Envious-Data/Env-KB/_pictures/Rev.0/Built/DSC_0819.JPG

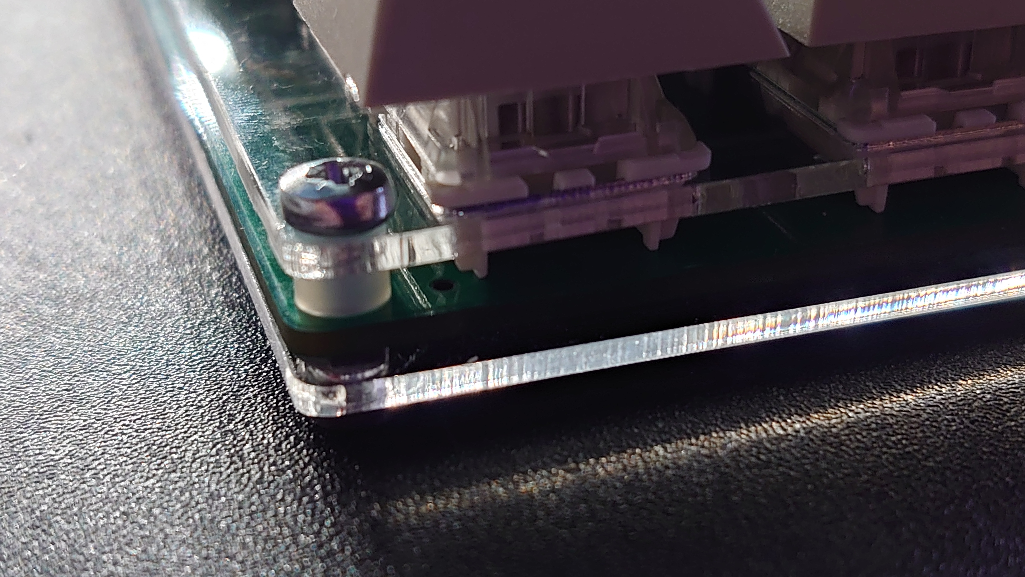
_pictures/Rev.0/Built/DSC_0819.JPG
