Envious-Data/Env-KB/_pictures/Rev.0/PCB2.JPG

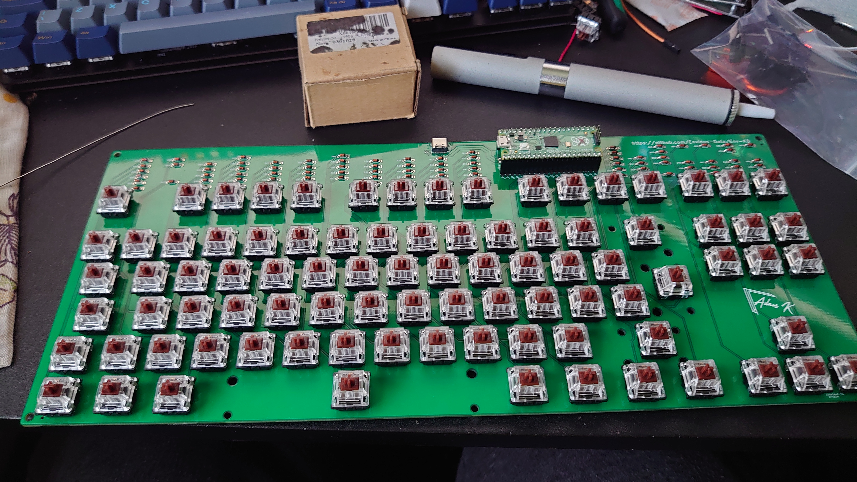
_pictures/Rev.0/PCB2.JPG
