Envious-Data/Env-KB/_pictures/Rev.0/PCB4.JPG

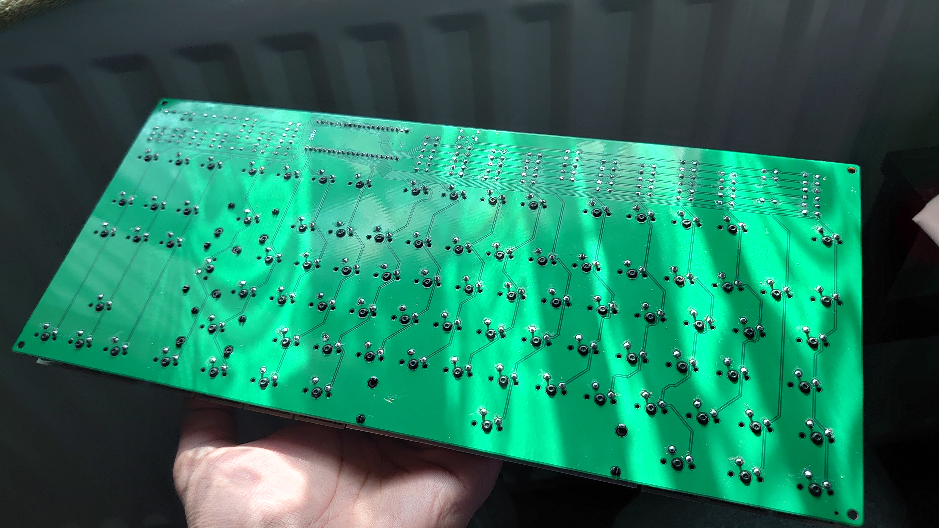
_pictures/Rev.0/PCB4.JPG
