Envious-Data/Env-KB/_pictures/Rev.0/PCB7.JPG

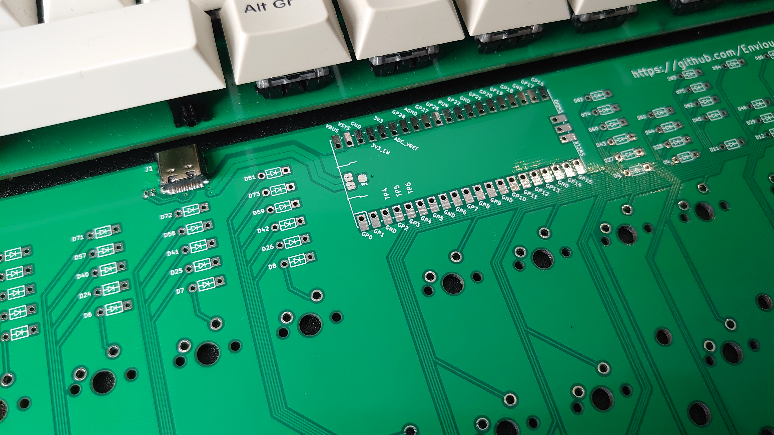
_pictures/Rev.0/PCB7.JPG
