Envious-Data/Env-KB/_pictures/Rev.0/PCB9.JPG

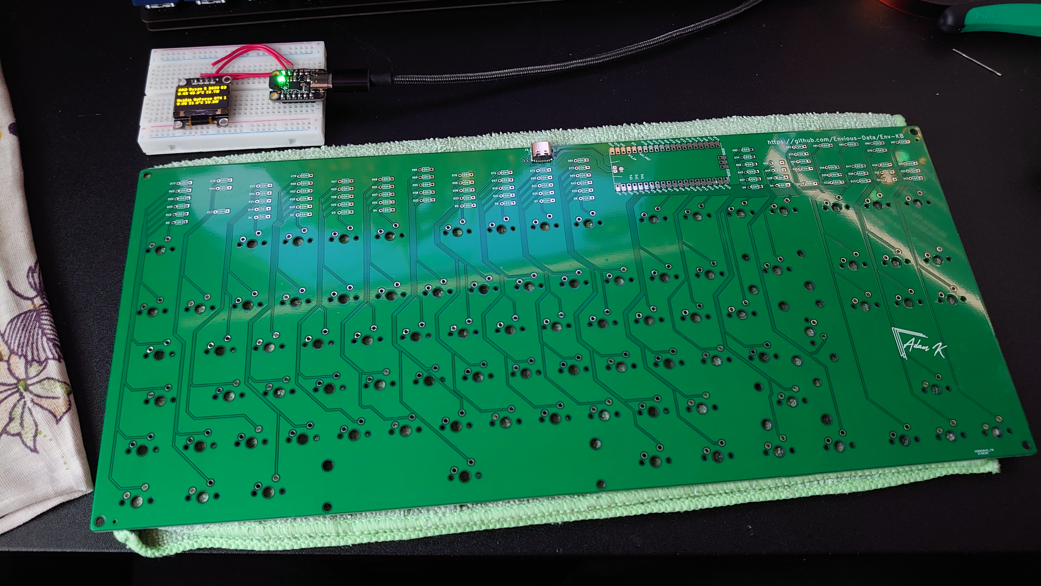
_pictures/Rev.0/PCB9.JPG
