Envious-Data/Env-KB/_pictures/Rev.0/PCB11.jpg

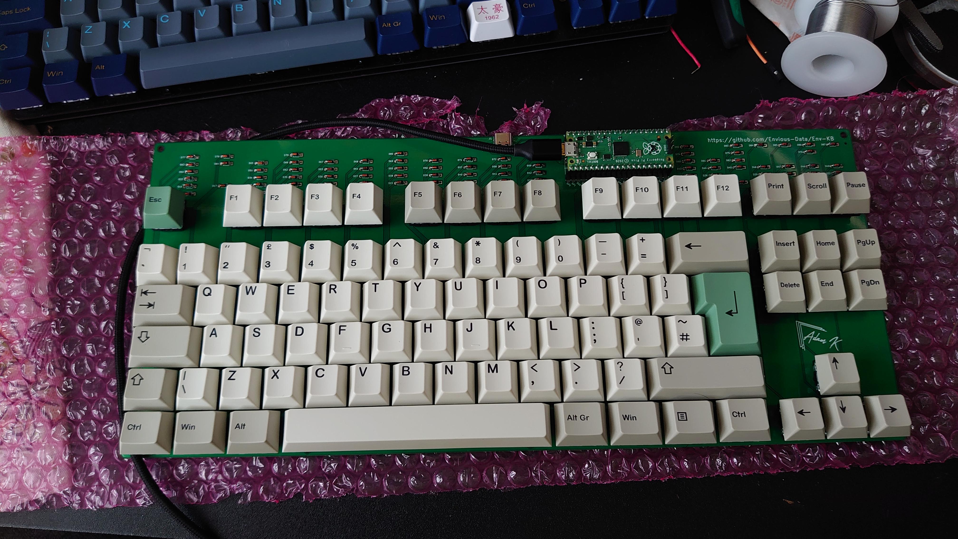
_pictures/Rev.0/PCB11.jpg
